palmerr23/ESP32-PSU/ESP32_LCD_Breakout_OWM_2-8_V1/arial.h

#ifndef arial_h
#define arial_h

// Arial_round_16x24.c
// Font type    : Full (95 characters)
// Font size    : 16x24 pixels
// Memory usage : 4564 bytes

const uint8_t arial_font[]={   //width, height, start char, # chars
//0x10,0x18,0x20,0x5F,
0x10,0x18,0x20,0x60,    //degrees added manually to codepoint 0x7F
0x00,0x00,0x00,0x00,0x00,0x00,0x00,0x00,0x00,0x00,0x00,0x00,0x00,0x00,0x00,0x00,0x00,0x00,0x00,0x00,0x00,0x00,0x00,0x00,0x00,0x00,0x00,0x00,0x00,0x00,0x00,0x00,0x00,0x00,0x00,0x00,0x00,0x00,0x00,0x00,0x00,0x00,0x00,0x00,0x00,0x00,0x00,0x00,  // <space>
0x01,0x80,0x03,0xC0,0x03,0xC0,0x03,0xC0,0x03,0xC0,0x03,0xC0,0x03,0xC0,0x03,0xC0,0x03,0xC0,0x03,0x80,0x01,0x80,0x01,0x80,0x01,0x80,0x00,0x00,0x00,0x00,0x01,0x80,0x03,0xC0,0x03,0xC0,0x01,0x80,0x00,0x00,0x00,0x00,0x00,0x00,0x00,0x00,0x00,0x00,  // !
0x00,0x00,0x00,0x00,0x06,0x30,0x06,0x30,0x0C,0x60,0x0C,0x60,0x0E,0x70,0x0E,0x70,0x06,0x30,0x00,0x00,0x00,0x00,0x00,0x00,0x00,0x00,0x00,0x00,0x00,0x00,0x00,0x00,0x00,0x00,0x00,0x00,0x00,0x00,0x00,0x00,0x00,0x00,0x00,0x00,0x00,0x00,0x00,0x00,  // "
0x00,0x00,0x00,0x00,0x03,0x18,0x03,0x18,0x07,0x38,0x07,0x38,0x3F,0xFC,0x3F,0xFC,0x06,0x70,0x0E,0x70,0x0E,0x70,0x0E,0x60,0x3F,0xFC,0x3F,0xFC,0x1C,0xE0,0x1C,0xE0,0x1C,0xC0,0x18,0xC0,0x18,0xC0,0x00,0x00,0x00,0x00,0x00,0x00,0x00,0x00,0x00,0x00,  // #
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

0x00,0x00,0x00,0x00,0x1C,0x00,0x3E,0x00,0x63,0x00,0x63,0x00,0x63,0x00,0x3E,0x00,0x1C,0x00,0x00,0x00,0x00,0x00,0x00,0x00,0x00,0x00,0x00,0x00,0x00,0x00,0x00,0x00,0x00,0x00,0x00,0x00,0x00,0x00,0x00,0x00,0x00,0x00,0x00,0x00,0x00,0x00,0x00,0x00,  // degrees
};

#endif
