palmerr23/ESP32-PSU/ESP32_LCD_Breakout_OWM_2-8_V1/bigfont.h

#ifndef big_font_h
#define big_font_h
// BigFont.c (C)2010 by Henning Karlsen
// Font Size	: 16x16
// Memory usage	: 3044 bytes
// # characters	: 95

const uint8_t BigFont[] ={
0x10,0x10,0x20,0x60, //degrees added manually to codepoint 0x7F
0x00,0x00,0x00,0x00,0x00,0x00,0x00,0x00,0x00,0x00,0x00,0x00,0x00,0x00,0x00,0x00,0x00,0x00,0x00,0x00,0x00,0x00,0x00,0x00,0x00,0x00,0x00,0x00,0x00,0x00,0x00,0x00, //  <Space>
0x00,0x00,0x00,0x00,0x07,0x00,0x0F,0x80,0x0F,0x80,0x0F,0x80,0x0F,0x80,0x0F,0x80,0x07,0x00,0x07,0x00,0x00,0x00,0x00,0x00,0x07,0x00,0x07,0x00,0x07,0x00,0x00,0x00, // !
0x00,0x00,0x0E,0x38,0x0E,0x38,0x0E,0x38,0x0E,0x38,0x06,0x30,0x00,0x00,0x00,0x00,0x00,0x00,0x00,0x00,0x00,0x00,0x00,0x00,0x00,0x00,0x00,0x00,0x00,0x00,0x00,0x00, // "
0x00,0x00,0x0C,0x30,0x0C,0x30,0x0C,0x30,0x7F,0xFE,0x7F,0xFE,0x0C,0x30,0x0C,0x30,0x0C,0x30,0x0C,0x30,0x7F,0xFE,0x7F,0xFE,0x0C,0x30,0x0C,0x30,0x0C,0x30,0x00,0x00, // #
0x00,0x00,0x02,0x40,0x02,0x40,0x0F,0xF8,0x1F,0xF8,0x1A,0x40,0x1A,0x40,0x1F,0xF0,0x0F,0xF8,0x02,0x58,0x02,0x58,0x1F,0xF8,0x1F,0xF0,0x02,0x40,0x02,0x40,0x00,0x00, // $
0x00,0x00,0x00,0x00,0x00,0x00,0x0E,0x10,0x0E,0x30,0x0E,0x70,0x00,0xE0,0x01,0xC0,0x03,0x80,0x07,0x00,0x0E,0x70,0x0C,0x70,0x08,0x70,0x00,0x00,0x00,0x00,0x00,0x00, // %
0x00,0x00,0x00,0x00,0x0F,0x00,0x19,0x80,0x19,0x80,0x19,0x80,0x0F,0x00,0x0F,0x08,0x0F,0x98,0x19,0xF8,0x18,0xF0,0x18,0xE0,0x19,0xF0,0x0F,0x98,0x00,0x00,0x00,0x00, // &
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
0x00,0x00,0x00,0x00,0x1C,0x00,0x3E,0x00,0x63,0x00,0x63,0x00,0x63,0x00,0x3E,0x00,0x1C,0x00,0x00,0x00,0x00,0x00,0x00,0x00,0x00,0x00,0x00,0x00,0x00,0x00,0x00,0x00  // degrees
}; 
#endif
