palmerr23/ESP32-PSU/ESP32_LCD_Breakout_OWM_2-8_V1/medfont.h

#ifndef med_font_h
#define med_font_h
// Font Size	: 8x12
// Memory usage	: 1144 bytes
// # characters	: 95

const uint8_t MedFont[] ={         
0x08,0x0C,0x20,0x5F,
0x00,0x00,0x00,0x00,0x00,0x00,0x00,0x00,0x00,0x00,0x00,0x00, // <Space>
0x00,0x00,0x20,0x20,0x20,0x20,0x20,0x20,0x00,0x20,0x00,0x00, // !
0x00,0x28,0x50,0x50,0x00,0x00,0x00,0x00,0x00,0x00,0x00,0x00, // "
0x00,0x00,0x28,0x28,0xFC,0x28,0x50,0xFC,0x50,0x50,0x00,0x00, // #
0x00,0x20,0x78,0xA8,0xA0,0x60,0x30,0x28,0xA8,0xF0,0x20,0x00, // $
0x00,0x00,0x48,0xA8,0xB0,0x50,0x28,0x34,0x54,0x48,0x00,0x00, // %
0x00,0x00,0x20,0x50,0x50,0x78,0xA8,0xA8,0x90,0x6C,0x00,0x00, // &
0x00,0x40,0x40,0x80,0x00,0x00,0x00,0x00,0x00,0x00,0x00,0x00, // '
0x00,0x04,0x08,0x10,0x10,0x10,0x10,0x10,0x10,0x08,0x04,0x00, // (
0x00,0x40,0x20,0x10,0x10,0x10,0x10,0x10,0x10,0x20,0x40,0x00, // )
0x00,0x00,0x00,0x20,0xA8,0x70,0x70,0xA8,0x20,0x00,0x00,0x00, // *
0x00,0x00,0x20,0x20,0x20,0xF8,0x20,0x20,0x20,0x00,0x00,0x00, // +
0x00,0x00,0x00,0x00,0x00,0x00,0x00,0x00,0x00,0x40,0x40,0x80, // ,
0x00,0x00,0x00,0x00,0x00,0xF8,0x00,0x00,0x00,0x00,0x00,0x00, // -
0x00,0x00,0x00,0x00,0x00,0x00,0x00,0x00,0x00,0x40,0x00,0x00, // .
0x00,0x08,0x10,0x10,0x10,0x20,0x20,0x40,0x40,0x40,0x80,0x00, // /
0x00,0x00,0x70,0x88,0x88,0x88,0x88,0x88,0x88,0x70,0x00,0x00, // 0
0x00,0x00,0x20,0x60,0x20,0x20,0x20,0x20,0x20,0x70,0x00,0x00, // 1
0x00,0x00,0x70,0x88,0x88,0x10,0x20,0x40,0x80,0xF8,0x00,0x00, // 2
0x00,0x00,0x70,0x88,0x08,0x30,0x08,0x08,0x88,0x70,0x00,0x00, // 3
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
0x00,0x18,0x10,0x10,0x10,0x20,0x10,0x10,0x10,0x10,0x18,0x00, // {
0x10,0x10,0x10,0x10,0x10,0x10,0x10,0x10,0x10,0x10,0x10,0x10, // |
0x00,0x60,0x20,0x20,0x20,0x10,0x20,0x20,0x20,0x20,0x60,0x00, // }
0x40,0xA4,0x18,0x00,0x00,0x00,0x00,0x00,0x00,0x00,0x00,0x00, // ~
};  
#endif
