palmerr23/ESP32-PSU/source/Control_C_ADS_Touch_3_5/platylogo.h

const uint8_t pLogo [] PROGMEM = {
	// 'platy logo, 87x64px
	0x00, 0x00, 0x00, 0x00, 0x00, 0x00, 0x00, 0x00, 0x00, 0x00, 0x00, 0x00, 0x00, 0x00, 0x00, 0x00, 
	0x00, 0x00, 0x00, 0x00, 0x00, 0x00, 0x00, 0x00, 0x00, 0x00, 0xfe, 0x00, 0x00, 0x00, 0x00, 0x00, 
	0x00, 0x00, 0x00, 0x00, 0x0f, 0xff, 0xf0, 0x00, 0x00, 0x00, 0x00, 0x00, 0x00, 0x00, 0x00, 0x7f, 
	0xff, 0xfe, 0x00, 0x00, 0x00, 0x00, 0x00, 0x00, 0x00, 0x01, 0xff, 0xff, 0xff, 0x80, 0x00, 0x00, 
	0x00, 0x00, 0x00, 0x00, 0x03, 0xff, 0xff, 0xff, 0xe0, 0x00, 0x00, 0x00, 0x00, 0x00, 0x00, 0x0f, 
	0xff, 0xff, 0xff, 0xf8, 0x00, 0x00, 0x00, 0x00, 0x00, 0x00, 0x1f, 0xff, 0xff, 0xff, 0xfc, 0x00, 
	0x00, 0x00, 0x00, 0x00, 0x00, 0x3f, 0xff, 0xff, 0xff, 0xff, 0x00, 0x00, 0x00, 0x00, 0x00, 0x00, 
	0x7f, 0xff, 0xff, 0xff, 0xff, 0x80, 0x00, 0x00, 0x00, 0x00, 0x00, 0x7f, 0xff, 0xff, 0xff, 0xff, 
	0x80, 0x00, 0x00, 0x00, 0x00, 0x00, 0xff, 0xff, 0xff, 0xff, 0xff, 0xc0, 0x00, 0x00, 0x00, 0x00, 
	0x00, 0xff, 0xff, 0xff, 0xff, 0xff, 0xf0, 0x00, 0x00, 0x00, 0x00, 0x01, 0xff, 0xff, 0xff, 0xff, 
	0xff, 0xf0, 0x00, 0x00, 0x00, 0x00, 0x01, 0xff, 0xff, 0xff, 0xff, 0xff, 0xf0, 0x00, 0x00, 0x00, 
	0x00, 0x03, 0xff, 0xff, 0xff, 0xff, 0xff, 0xdf, 0xc0, 0x00, 0x00, 0x00, 0x03, 0xff, 0xff, 0xff, 
	0xff, 0xff, 0xff, 0xf0, 0x00, 0x00, 0x00, 0x03, 0xff, 0xff, 0xff, 0xff, 0xfe, 0xff, 0xfc, 0x00, 
	0x00, 0x00, 0x07, 0xff, 0xff, 0xff, 0xff, 0xfe, 0xff, 0xfe, 0x00, 0x00, 0x00, 0x07, 0xff, 0xff, 
	0xff, 0xff, 0xfd, 0xff, 0xff, 0x00, 0x00, 0x00, 0x07, 0xff, 0xff, 0xff, 0xff, 0xff, 0xff, 0xff, 
	0x80, 0x00, 0x00, 0x07, 0xff, 0xff, 0xff, 0xff, 0xfb, 0xff, 0xff, 0xc0, 0x00, 0x00, 0x0f, 0xff, 
	0xff, 0xff, 0xff, 0xfb, 0xff, 0xff, 0xc0, 0x00, 0x00, 0x1f, 0xff, 0xff, 0xff, 0xff, 0xff, 0xff, 
	0xff, 0xe0, 0x00, 0x00, 0x1b, 0xff, 0xff, 0xff, 0xff, 0xff, 0xff, 0xff, 0xe0, 0x00, 0x00, 0x3b, 
	0xff, 0xff, 0xff, 0xff, 0xf7, 0xff, 0xff, 0xe0, 0x00, 0x00, 0x7d, 0xff, 0xff, 0xff, 0xff, 0xf7, 
	0xff, 0xff, 0xf0, 0x00, 0x00, 0x7f, 0xff, 0xff, 0xff, 0xff, 0xff, 0xfc, 0xff, 0xf4, 0x00, 0x00, 
	0xfe, 0xff, 0xff, 0xc0, 0x7f, 0xfb, 0xff, 0x7f, 0xff, 0xc0, 0x01, 0xff, 0x7f, 0xff, 0x80, 0x07, 
	0xfb, 0xff, 0x7f, 0xff, 0xf0, 0x01, 0xff, 0x9f, 0xff, 0x80, 0x03, 0xfb, 0xff, 0xff, 0xef, 0xe0, 
	0x03, 0xff, 0xe0, 0xff, 0x00, 0x03, 0xfd, 0xff, 0xf8, 0x6f, 0x80, 0x03, 0xff, 0xe0, 0xff, 0x00, 
	0x03, 0xfe, 0xff, 0x1f, 0xa6, 0x00, 0x07, 0xff, 0xe0, 0xfe, 0x00, 0x01, 0xfc, 0x7e, 0xff, 0xc0, 
	0x00, 0x07, 0xff, 0xc0, 0x7c, 0x00, 0x00, 0xfc, 0x3d, 0xff, 0xc0, 0x00, 0x07, 0xff, 0xc0, 0x7c, 
	0x00, 0x00, 0xf8, 0x0f, 0xff, 0xe0, 0x00, 0x0f, 0xff, 0xc0, 0x00, 0x00, 0x00, 0x78, 0x01, 0xff, 
	0xe0, 0x00, 0x0f, 0xff, 0xc0, 0x3c, 0x00, 0x00, 0x00, 0x01, 0xff, 0xe0, 0x00, 0x0f, 0xff, 0xc0, 
	0x3f, 0x00, 0x00, 0x78, 0x03, 0xff, 0xf0, 0x00, 0x0f, 0xff, 0xc0, 0x3f, 0x80, 0x00, 0x7c, 0x03, 
	0xff, 0xf8, 0x00, 0x1f, 0xff, 0xc0, 0x3f, 0xc0, 0x00, 0x7e, 0x03, 0xff, 0xf8, 0x00, 0x1f, 0xff, 
	0xc0, 0x3f, 0xe0, 0x00, 0x7f, 0x83, 0xff, 0xfe, 0x00, 0x1f, 0xff, 0xc0, 0x3f, 0xf0, 0x00, 0x7f, 
	0xc3, 0xff, 0xff, 0x00, 0x1f, 0xff, 0xc0, 0x3f, 0xf0, 0x00, 0x7f, 0xe0, 0xf8, 0x3e, 0x00, 0x1f, 
	0xff, 0xc0, 0x3f, 0xc0, 0x00, 0x7f, 0xe0, 0x00, 0x00, 0x00, 0x1f, 0xff, 0xe0, 0x3b, 0x40, 0x00, 
	0x7f, 0xc0, 0x00, 0x00, 0x00, 0x1f, 0xff, 0xe0, 0x10, 0x00, 0x00, 0x7f, 0x80, 0x00, 0x00, 0x00, 
	0x1f, 0xff, 0xe0, 0x00, 0x00, 0x00, 0x7c, 0x80, 0x00, 0x00, 0x00, 0x1f, 0xff, 0xf0, 0x00, 0x00, 
	0x00, 0x08, 0x00, 0x00, 0x00, 0x00, 0x1f, 0xff, 0xf0, 0x00, 0x00, 0x00, 0x00, 0x00, 0x00, 0x00, 
	0x00, 0x0f, 0xff, 0xf0, 0x00, 0x00, 0x00, 0x00, 0x00, 0x00, 0x00, 0x00, 0x0f, 0xff, 0xf8, 0x00, 
	0x00, 0x00, 0x00, 0x00, 0x00, 0x00, 0x00, 0x0f, 0xff, 0xf8, 0x00, 0x00, 0x00, 0x00, 0x00, 0x00, 
	0x00, 0x00, 0x07, 0xff, 0xf8, 0x00, 0x00, 0x00, 0x00, 0x00, 0x00, 0x00, 0x00, 0x07, 0xff, 0xf8, 
	0x00, 0x00, 0x00, 0x00, 0x00, 0x00, 0x00, 0x00, 0x03, 0xff, 0xf8, 0x00, 0x00, 0x00, 0x00, 0x00, 
	0x00, 0x00, 0x00, 0x01, 0xff, 0xf8, 0x00, 0x00, 0x00, 0x00, 0x00, 0x00, 0x00, 0x00, 0x01, 0xff, 
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
};
