palmerr23/ESP32-PSU/ESP32_LCD_Breakout_OWM_2-8_V1/small_font.h

#ifndef small_font_h
#define small_font_h

// mykefont2.c
// Font type    : Full (95 characters)
// Font size    : 8x9 pixels
// Memory usage : 859 bytes

const uint8_t myke_font[]={   //width, height, start char, # chars
0x08,0x09,0x20,0x5F,
0x00,0x00,0x00,0x00,0x00,0x00,0x00,0x00,0x00,  // <space>
0x00,0x10,0x10,0x10,0x10,0x00,0x00,0x10,0x00,  // !
0x00,0x50,0x50,0x50,0x00,0x00,0x00,0x00,0x00,  // "
0x00,0x00,0x28,0x7C,0x28,0x7C,0x28,0x00,0x00,  // #
0x10,0x3C,0x50,0x50,0x38,0x14,0x14,0x78,0x10,  // $
0x00,0xE2,0xA4,0xA8,0xEE,0x1A,0x2A,0x4E,0x00,  // %
0x00,0x38,0x48,0x38,0x20,0x54,0x4C,0x7A,0x00,  // &
0x00,0x40,0x40,0x40,0x00,0x00,0x00,0x00,0x00,  // '
0x10,0x10,0x20,0x20,0x20,0x20,0x20,0x10,0x10,  // (
0x20,0x20,0x10,0x10,0x10,0x10,0x10,0x20,0x20,  // )
0x20,0x70,0x70,0x20,0x00,0x00,0x00,0x00,0x00,  // *
0x00,0x00,0x10,0x10,0x7C,0x10,0x10,0x00,0x00,  // +
0x00,0x00,0x00,0x00,0x00,0x00,0x10,0x10,0x20,  // ,
0x00,0x00,0x00,0x00,0x00,0x38,0x00,0x00,0x00,  // -
0x00,0x00,0x00,0x00,0x00,0x00,0x00,0x10,0x00,  // .
0x08,0x08,0x10,0x10,0x10,0x20,0x20,0x40,0x40,  // /

0x00,0x00,0x38,0x48,0x48,0x48,0x48,0x48,0x70,  // 0
0x00,0x00,0x30,0x50,0x10,0x10,0x10,0x10,0x78,  // 1
0x00,0x00,0x30,0x48,0x08,0x18,0x10,0x20,0x78,  // 2
0x00,0x00,0x78,0x08,0x08,0x30,0x08,0x08,0x70,  // 3
0x00,0x00,0x18,0x28,0x68,0x48,0x7C,0x08,0x08,  // 4
0x00,0x00,0x78,0x40,0x40,0x70,0x08,0x08,0x70,  // 5
0x00,0x00,0x38,0x40,0x40,0x78,0x48,0x48,0x30,  // 6
0x00,0x00,0x7C,0x0C,0x08,0x18,0x10,0x30,0x20,  // 7
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
0x00,0x00,0x00,0x00,0x78,0x10,0x30,0x60,0x78,  // z
0x08,0x10,0x10,0x10,0x20,0x10,0x10,0x10,0x08,  // {
0x10,0x10,0x10,0x10,0x10,0x10,0x10,0x10,0x10,  // |
0x20,0x10,0x10,0x10,0x08,0x10,0x10,0x10,0x20,  // }
0x00,0x00,0x74,0x5C,0x00,0x00,0x00,0x00,0x00,  // ~
};

#endif
