palmerr23/ESP32-PSU/ESP32_LCD_Breakout_OWM_2-8_V1/graphics.h

#ifndef graphics_h
#define graphics_h
const uint8_t wifi[]={
  32,32,
  0x00,0x00,0x00,0x00
  ,0x00,0x00,0x00,0x00
  ,0x00,0x00,0x00,0x00
  ,0x00,0x0f,0xf0,0x00
  ,0x00,0x7f,0xfe,0x00
  ,0x03,0xff,0xff,0xc0
  ,0x07,0xff,0xff,0xe0
  ,0x1f,0xfe,0x7f,0xf8
  ,0x3f,0xc0,0x03,0xfc
  ,0x7f,0x00,0x00,0xfe
  ,0xfe,0x00,0x00,0x7f
  ,0xf8,0x07,0xe0,0x1f
  ,0xf0,0x3f,0xfc,0x0f
  ,0x60,0x7f,0xfe,0x06
  ,0x01,0xff,0xff,0x80
  ,0x03,0xfe,0x7f,0xc0
  ,0x03,0xf0,0x0f,0xc0
  ,0x07,0xe0,0x07,0xe0
  ,0x07,0xc0,0x03,0xe0
  ,0x03,0x83,0xc1,0xc0
  ,0x00,0x07,0xe0,0x00
  ,0x00,0x0f,0xf0,0x00
  ,0x00,0x1f,0xf8,0x00
  ,0x00,0x1f,0xf8,0x00
  ,0x00,0x1f,0xf8,0x00
  ,0x00,0x1f,0xf8,0x00
  ,0x00,0x0f,0xf0,0x00
  ,0x00,0x07,0xe0,0x00
  ,0x00,0x03,0xc0,0x00
  ,0x00,0x00,0x00,0x00
  ,0x00,0x00,0x00,0x00
  ,0x00,0x00,0x00,0x00
};
#endif
